Yorev89/Poly-Synth/docs/images/Synth Board.jpg

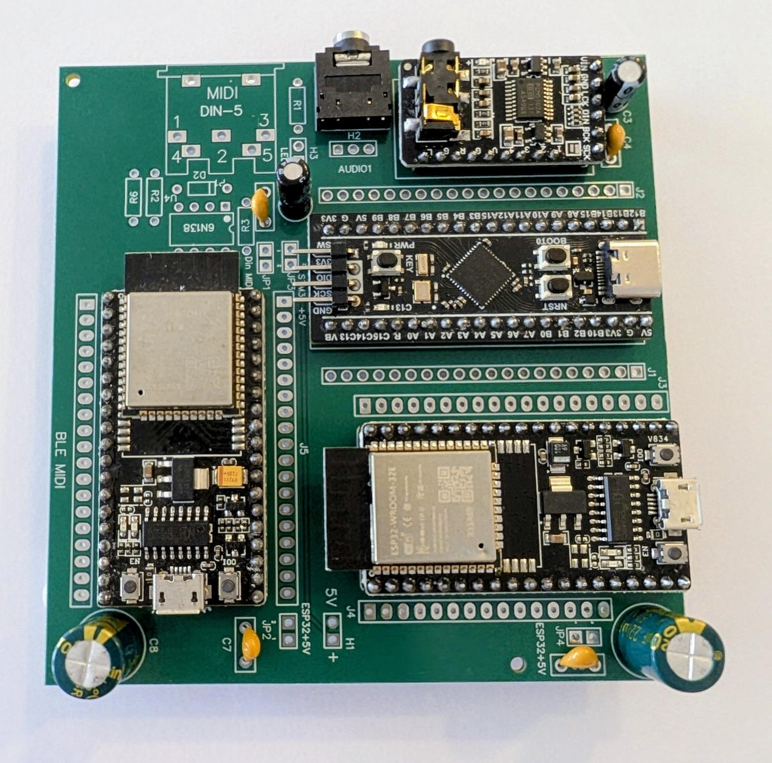
docs/images/Synth Board.jpg
