Yorev89/Poly-Synth/Hardware/PCB/PCB Components Layout.png

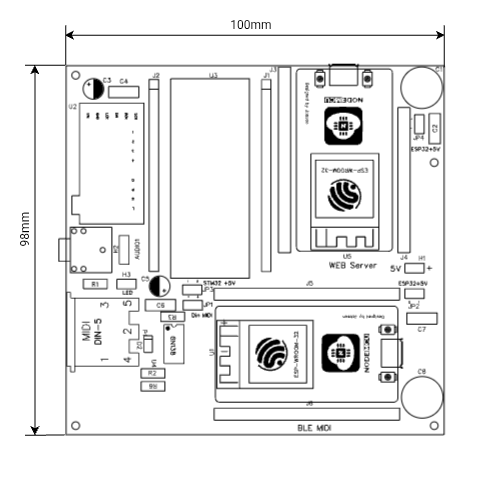
Hardware/PCB/PCB Components Layout.png
